Cidekar/ai-stoplight/firmware/test/stubs/Wire.h

// Wire.h - the sketch includes this for I2C setup. Everything it needs is
// already declared in the Arduino stub, so this only has to exist.
#ifndef STOPLIGHT_TEST_WIRE_H
#define STOPLIGHT_TEST_WIRE_H

#include "Arduino.h"

#endif  // STOPLIGHT_TEST_WIRE_H
